kati94/WRO-POLARIS/models/07.stl

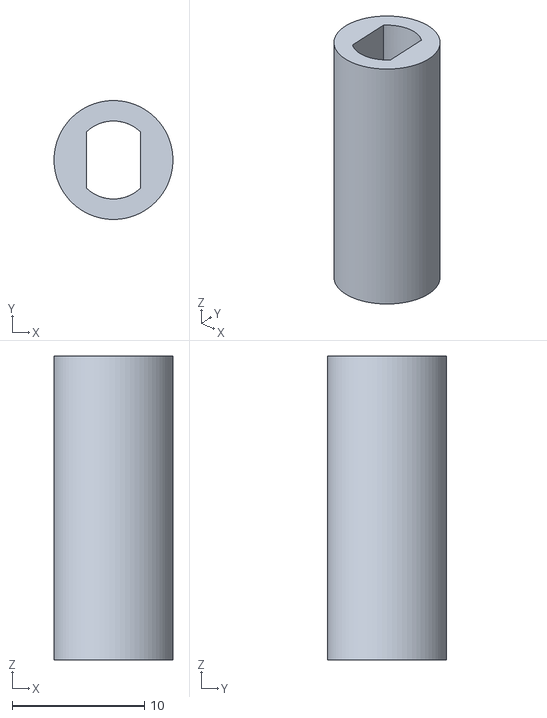
[picture p19: CAD file, 2026-06-18]
models/07.stl
9.00 x 9.00 x 23.0
