kati94/WRO-POLARIS/models/31.stl

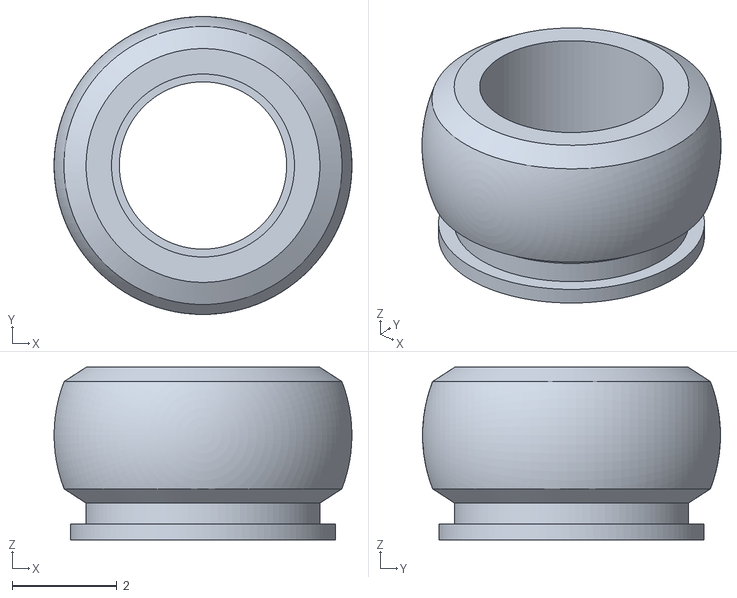
[picture p20: CAD file, 2026-06-18]
models/31.stl
5.70 x 5.70 x 3.30
