kati94/WRO-POLARIS/models/03.stl

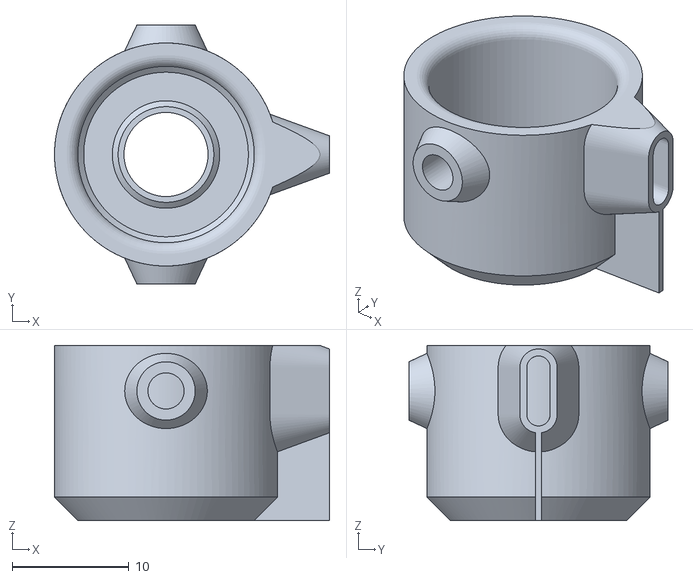
[picture p21: CAD file, 2026-06-18]
models/03.stl
23.6 x 22.2 x 15.0
