kati94/WRO-POLARIS/models/Ram_3.stl

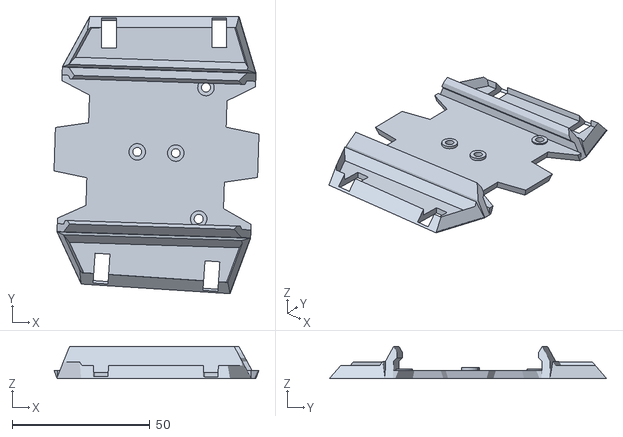
[picture p22: CAD file, 2026-06-18]
models/Ram_3.stl
74.5 x 100.8 x 11.7
