kati94/WRO-POLARIS/models/Pneu.stl

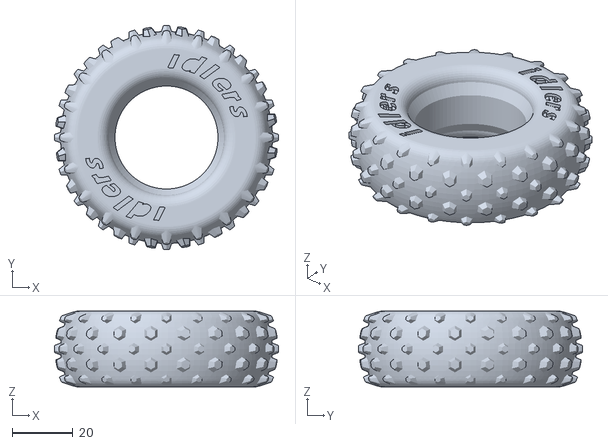
[picture p23: CAD file, 2026-06-18]
models/Pneu.stl
74.0 x 74.0 x 25.0
