kati94/WRO-POLARIS/models/21.stl

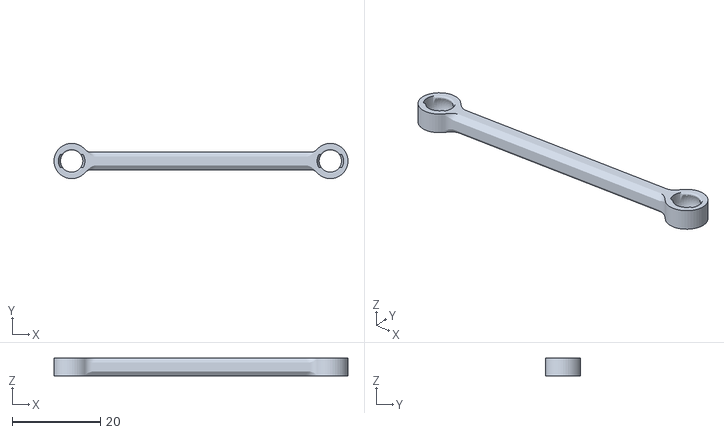
[picture p24: CAD file, 2026-06-18]
models/21.stl
66.6 x 8.00 x 4.00
