kati94/WRO-POLARIS/models/06.stl

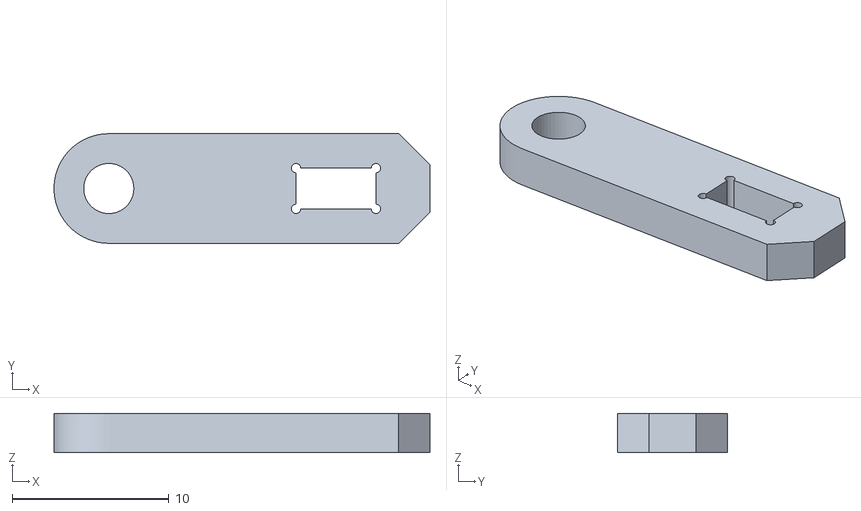
[picture p25: CAD file, 2026-06-18]
models/06.stl
24.0 x 7.00 x 2.50
