kati94/WRO-POLARIS/models/01.stl

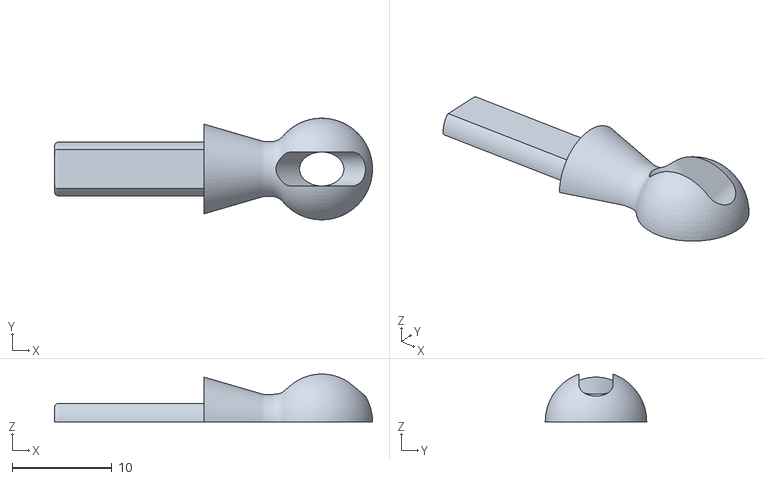
[picture p26: CAD file, 2026-06-18]
models/01.stl
31.9 x 10.2 x 4.80
